Kaibab11/MacroPad/PCB_FIles/Schematic Prints/Kpad_PCB Print/PCB Prints (seperate PDFs)/PCB Prints-5.pdf

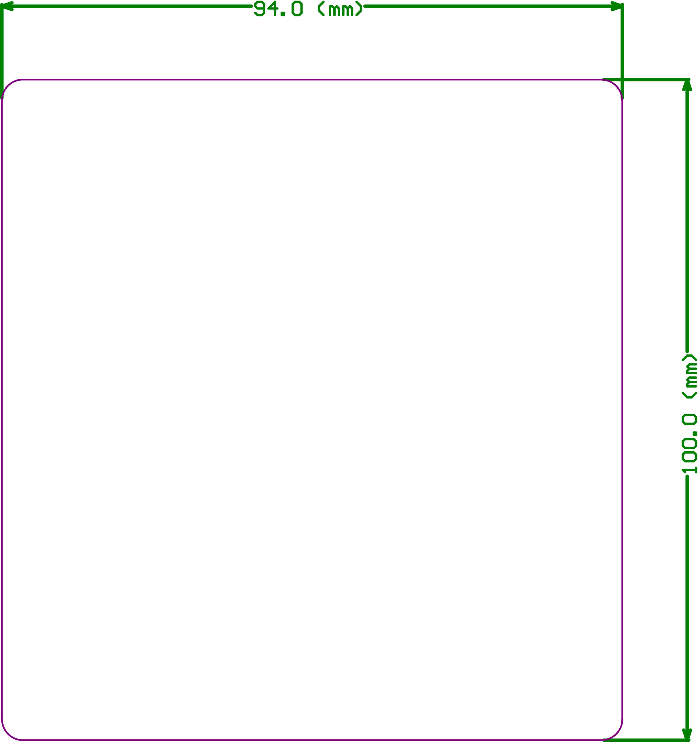
[picture p12: figure]
